piofthings/mini-mecanum/dev/pi/samples/foo.jpg

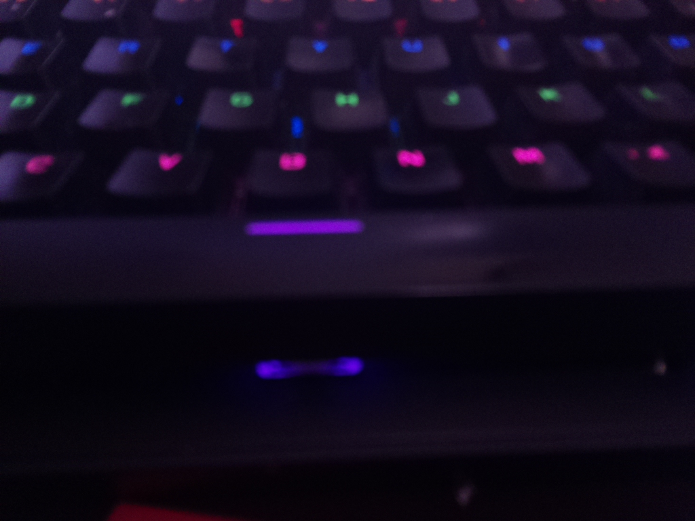
dev/pi/samples/foo.jpg
